kittennbfive/curious-kitten-JTAG/firmware/4067.h

#ifndef __4067_H__
#define __4067_H__
#include <stdint.h>
#include <stdbool.h>

/*
This file is part of curious-kitten-JTAG.

(c) 2022 by kittennbfive

AGPLv3+ and NO WARRANTY!
*/

void select_channel_4067_activate(const uint8_t ch, const bool half_vcc);

#endif
